csvanholm/Westinghouse-12KW-transfer-switch/Kicad schematic/westinghouse generator controller.kicad_sch

## KiCad design Kicad schematic/westinghouse generator controller.kicad_sch (2023-02-16)

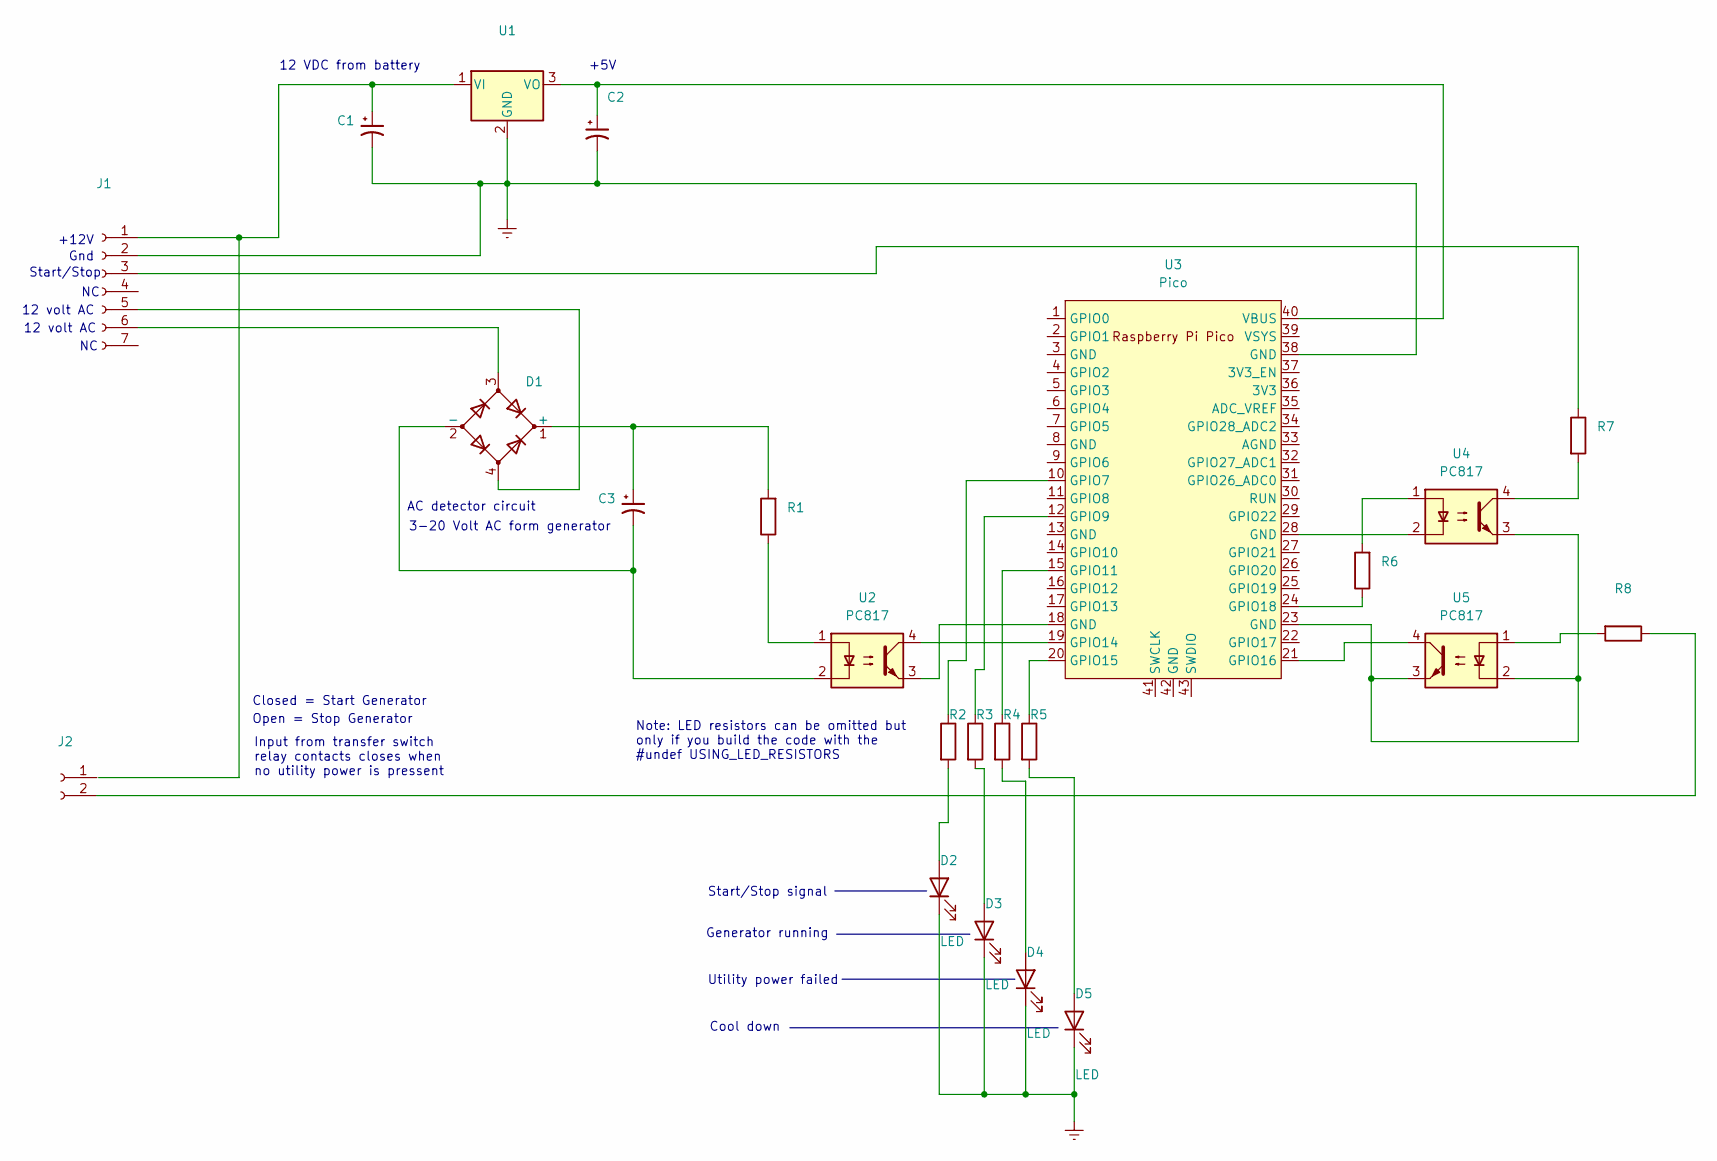
[picture p2: schematic westinghouse generator controller.kicad_sch]

Parts:
C1, C2: CP_Radial_D6.3mm_P2.50mm
C3: CP_Radial_D5.0mm_P2.50mm
D1: Diode_Bridge_Round_D9.8mm
D2, D3, D4, D5: LED; LED_D3.0mm_Horizontal_O3.81mm_Z10.0mm
J1: PinHeader_1x07_P1.00mm_Vertical
J2: PinHeader_1x02_P1.00mm_Vertical
R1, R2, R3, R4, R5, R6, R7, R8: R_Axial_DIN0309_L9.0mm_D3.2mm_P20.32mm_Horizontal
U1: TO-220-3_Vertical
U2, U4, U5: PC817; DIP-4_W7.62mm
U3: Pico; RPi_Pico_SMD_TH

Connections:
Earth: C1.2, C2.2, D2.1 (K), D3.1 (K), D4.1 (K), D5.1 (K), J1.2, U1.2 (GND), U3.38 (GND)
unnamed: C1.1, J1.1, U1.1 (VI)
unnamed: C2.1, U1.3 (VO), U3.40 (VBUS)
unnamed: C3.1, D1.1 (+), R1.2
unnamed: C3.2, D1.2 (-), U2.2
unnamed: D1.3, J1.6
unnamed: D1.4, J1.5
unnamed: D2.2 (A), R2.2
unnamed: D3.2 (A), R3.2
unnamed: D4.2 (A), R4.2
unnamed: D5.2 (A), R5.2
unnamed: J1.3, R7.1
unnamed: J2.2, R8.1
unnamed: R1.1, U2.1
unnamed: R2.1, U3.10 (GPIO7)
unnamed: R3.1, U3.12 (GPIO9)
unnamed: R4.1, U3.15 (GPIO11)
unnamed: R5.1, U3.20 (GPIO15)
unnamed: R6.1, U3.24 (GPIO18)
unnamed: R6.2, U4.1
unnamed: R7.2, U4.4
unnamed: R8.2, U5.1
unnamed: U2.3, U3.18 (GND)
unnamed: U2.4, U3.19 (GPIO14)
unnamed: U3.21 (GPIO16), U5.4
unnamed: U3.23 (GND), U4.3, U5.2, U5.3
unnamed: U3.28 (GND), U4.2

Notes on the sheet:
Start/Stop signal
AC detector circuit
12 volt AC
Open = Stop Generator
Cool down
Start/Stop
Input from transfer switch relay contacts closes when no utility power is pressent
Utility power failed
+12V
Closed = Start Generator
3-20 Volt AC form generator
Gnd
Generator running
+5V
Note: LED resistors can be omitted but only if you build the code with the #undef USING_LED_RESISTORS
12 VDC from battery
